amosyu2000/cyclops/src/capture_thread/README.md

<div align="center">

# Capture Button

</div>

## Hardware
[Normally Open Push Button](https://www.amazon.ca/Cylewet-Momentary-Button-Switch-CLT1078/dp/B07DS6QMRW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)

## Usage
In the `src` directory, run `pipenv run python -m capture_thread.__init__`
