amosyu2000/cyclops/docs/Presentations/Rev0Presentation/Rev0_Demo_Slides.pdf

# Cyclops

Real-time bicycle crash detection and blindspot monitoring.

MECHTRON 4TB6 | Rev0 Demo | GitHub (https://github.com/amosyu2000/cyclops) | Team 9 | 1

# What Cyclops offers

1.

### Blindspot Monitoring

MECHTRON 4TB6 | Rev0 Demo | GitHub (https://github.com/amosyu2000/cyclops) | Team 9 | 2

2.

### Convenient Mounting

3.

### Crash Detection

4.

### Video Export

# Blindspot Monitoring

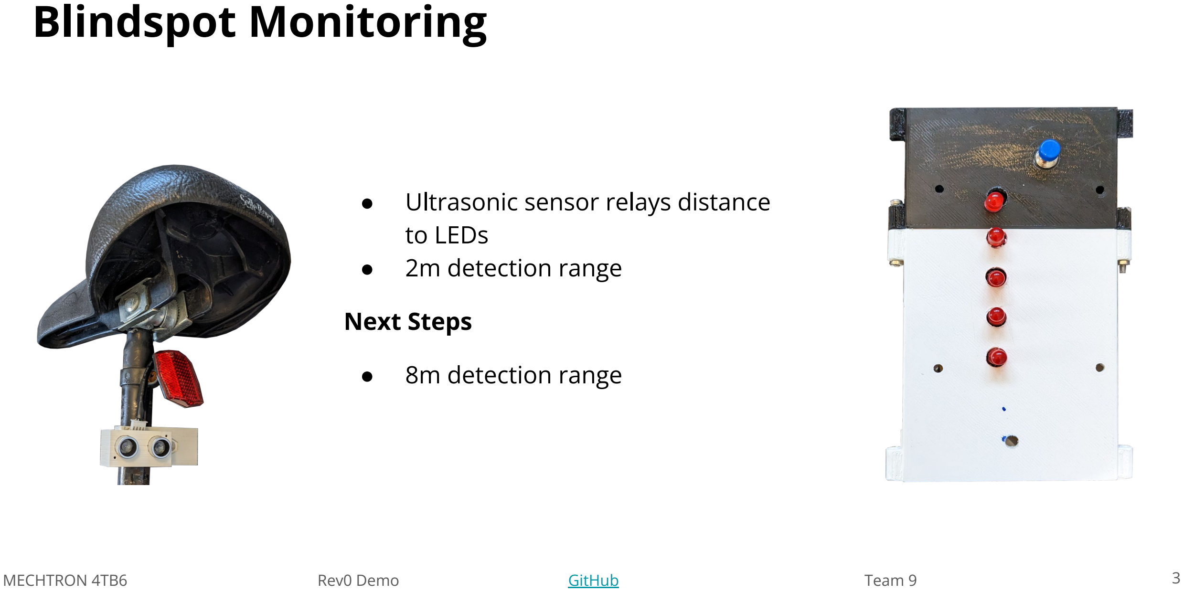
[picture p41: page 3]

- Ultrasonic sensor relays distance to LEDs
- 2m detection range
Next Steps
- 8m detection range
MECHTRON 4TB6 | Rev0 Demo | GitHub (https://github.com/amosyu2000/cyclops) | Team 9 | 3

# Blindspot Monitoring Algorithm

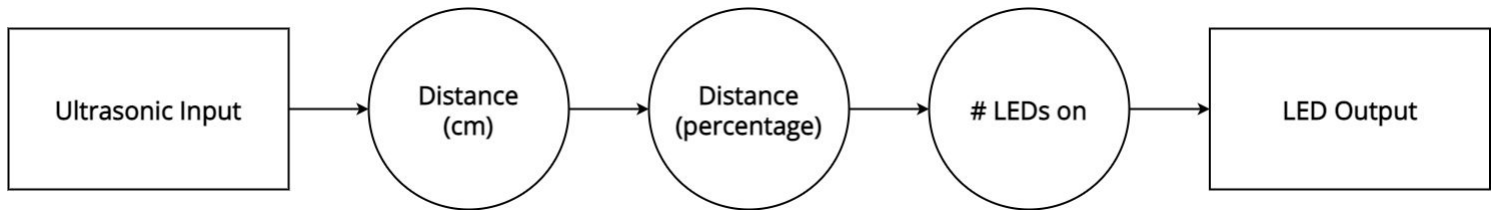
[picture p42: figure]

MECHTRON 4TB6 | Rev0 Demo | GitHub (https://github.com/amosyu2000/cyclops) | Team 9 | 4

# Convenient Mounting

- Turn nut to clamp/release housing
- Keeps together as a single unit
- Rubber grips

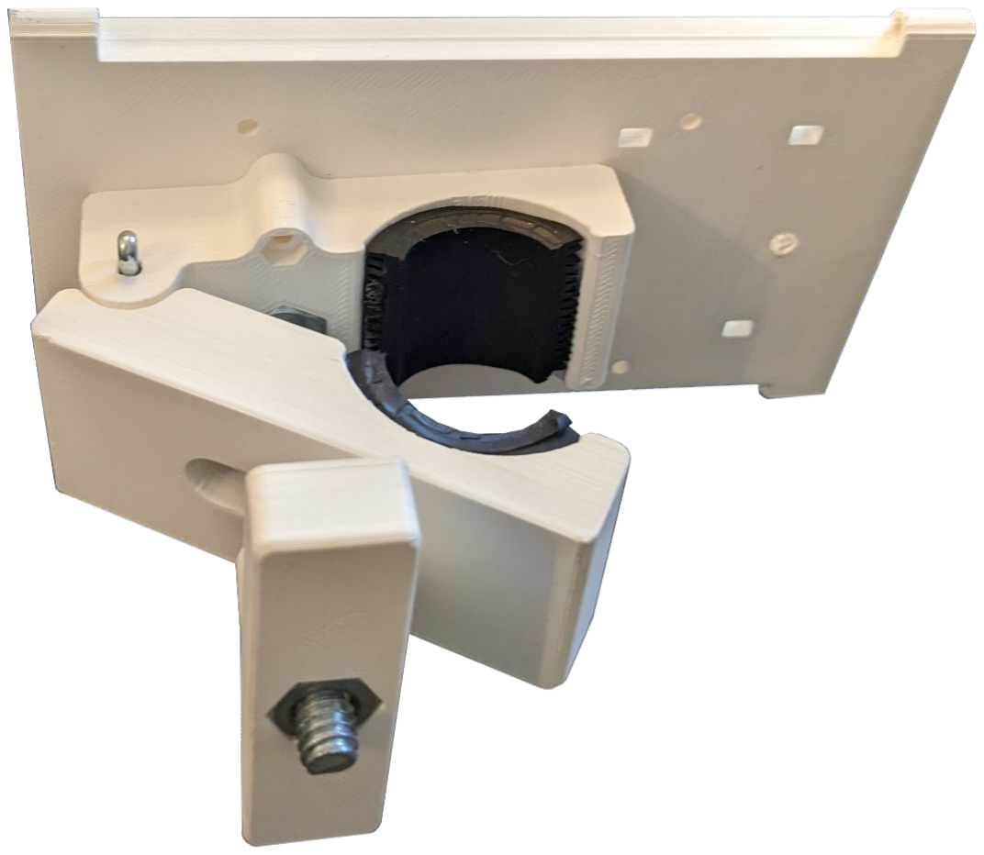
[picture p43: figure]

MECHTRON 4TB6 | Rev0 Demo | GitHub (https://github.com/amosyu2000/cyclops) | Team 9 | 5

# Crash Detection

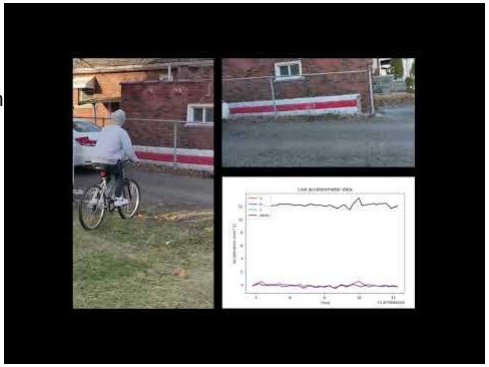
[picture p44: figure]

- Algorithm to interpret accelerometer readings (http://www.youtube.com/watch?v=p9dwgrGUkT8)
- On crash, 60% true positive rate
Next steps
- On crash, 95% true positive rate
- Eliminate false positives
MECHTRON 4TB6 | Rev0 Demo | GitHub (https://github.com/amosyu2000/cyclops) | Team 9 | 6

# Crash Detection Algorithm

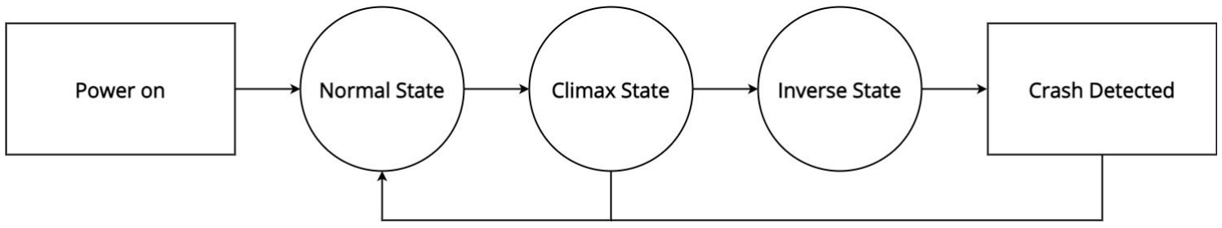
[picture p45: figure]

MECHTRON 4TB6 | Rev0 Demo | GitHub (https://github.com/amosyu2000/cyclops) | Team 9 | 7

# Video Export

- On crash or capture, saves last 60 seconds of video to disk
- Quality is 640p, 24fps
Next Steps
- Save video to thumb drive
- 720p, 30fps
- Decrease CPU utilization

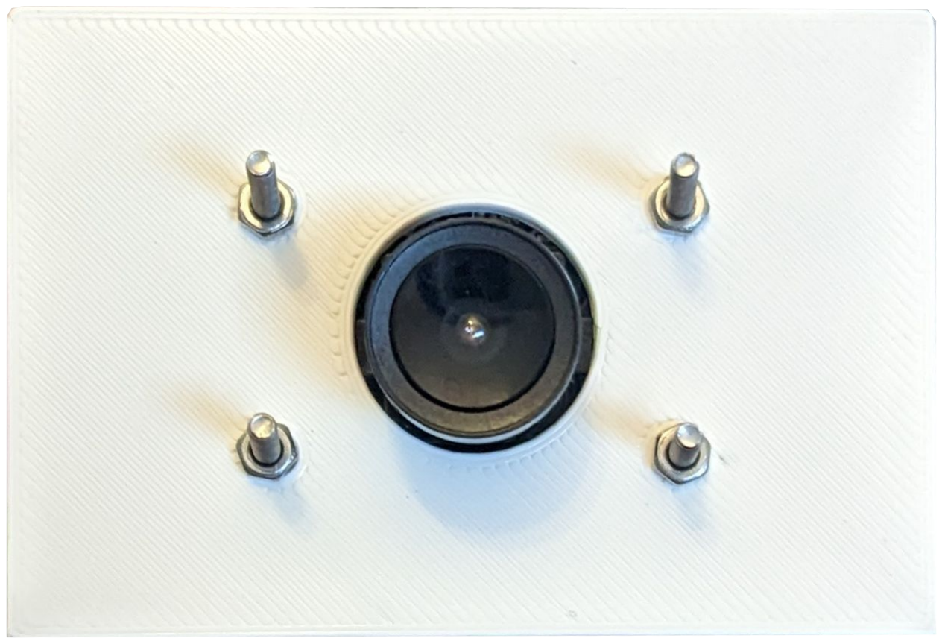
[picture p46: figure]

MECHTRON 4TB6 | Rev0 Demo | GitHub (https://github.com/amosyu2000/cyclops) | Team 9 | 8

# Video Export Algorithm

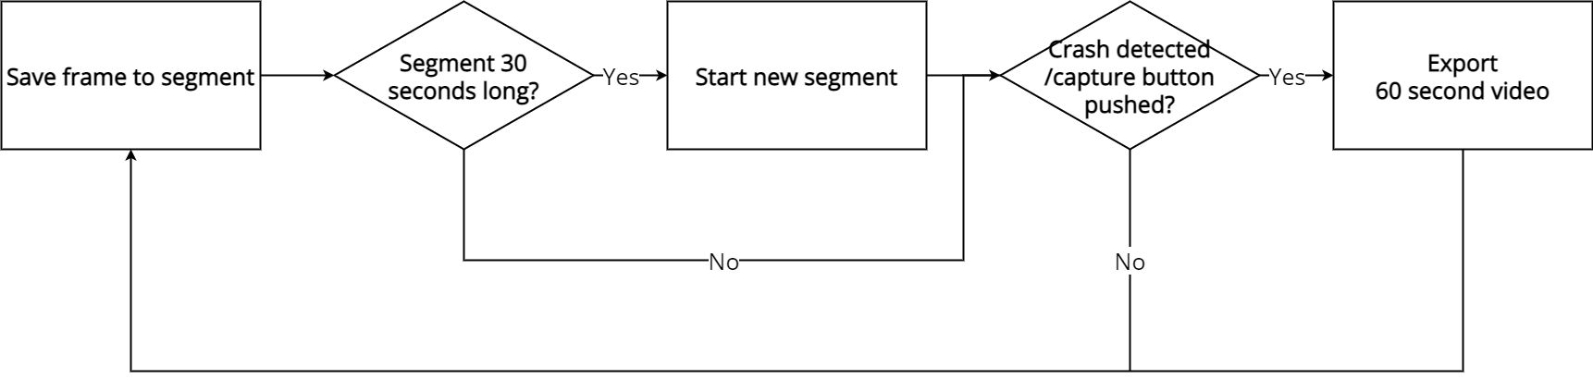
[picture p47: figure]

MECHTRON 4TB6 | Rev0 Demo | GitHub (https://github.com/amosyu2000/cyclops) | Team 9 | 9

# User Interface

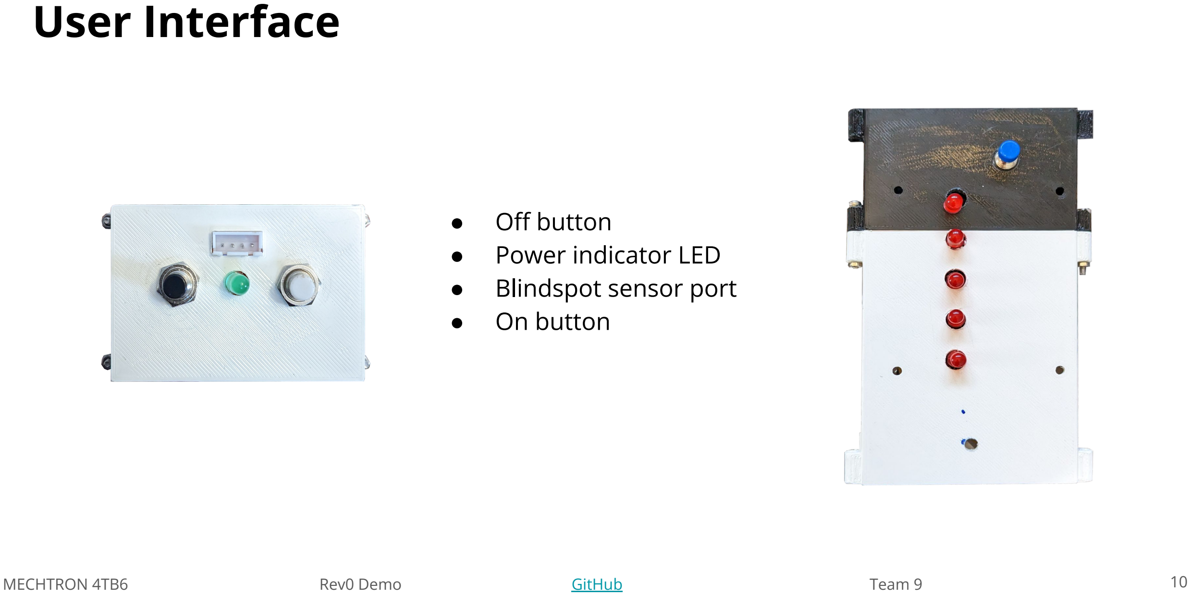
[picture p48: page 10]

- Off button
- Power indicator LED
- Blindspot sensor port
- On button
MECHTRON 4TB6 | Rev0 Demo | GitHub (https://github.com/amosyu2000/cyclops) | Team 9 | 10

# Installation

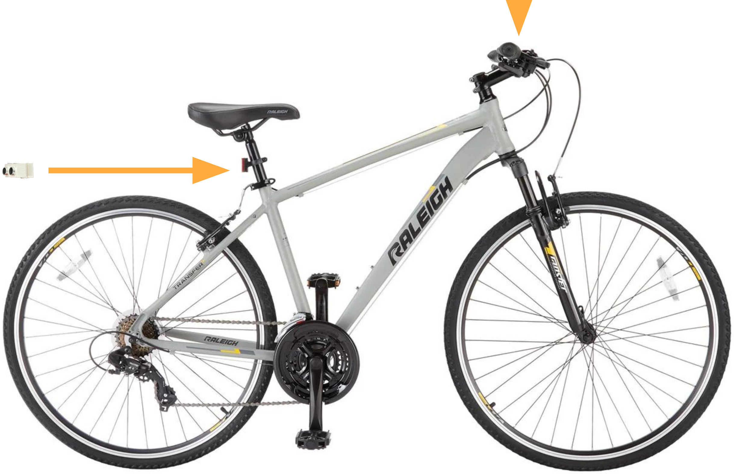
[picture p49: figure]

MECHTRON 4TB6 | Rev0 Demo | GitHub (https://github.com/amosyu2000/cyclops) | Team 9 | 11

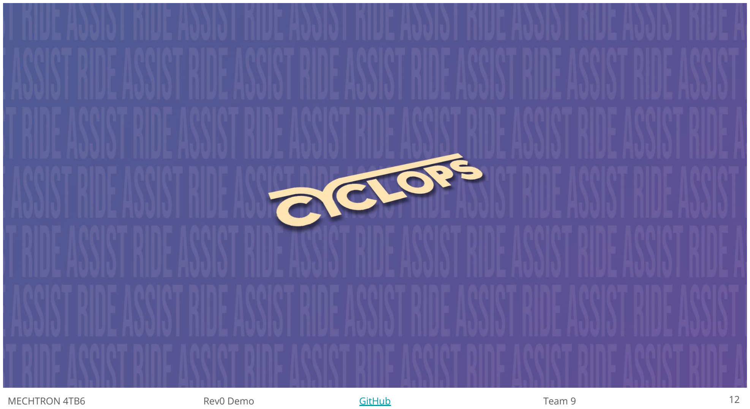
[picture p50: page 12]

MECHTRON 4TB6 | Rev0 Demo | GitHub (https://github.com/amosyu2000/cyclops) | Team 9 | 12
