amosyu2000/cyclops/src/lidar_thread/older_versions/ultrasonic_thread/README.md

<div align="center">

# Ultrasonic Sensor

</div>

## Hardware
[HC-SR04](https://pimylifeup.com/raspberry-pi-distance-sensor/)

## Usage
In the `src` directory, run `pipenv run python -m ultrasonic_thread.__init__`
