amosyu2000/cyclops/src/cad/RASPBERRY PI.stl

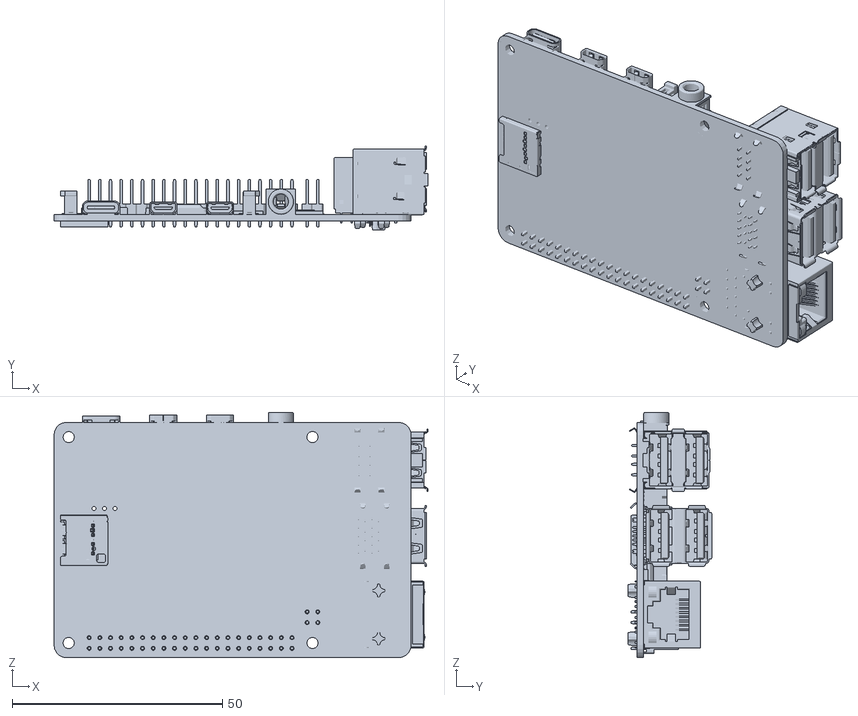
[picture p65: CAD file, 2023-04-05]
src/cad/RASPBERRY PI.stl
89.0 x 19.9 x 58.4
