amosyu2000/cyclops/src/cad/BOLT.stl

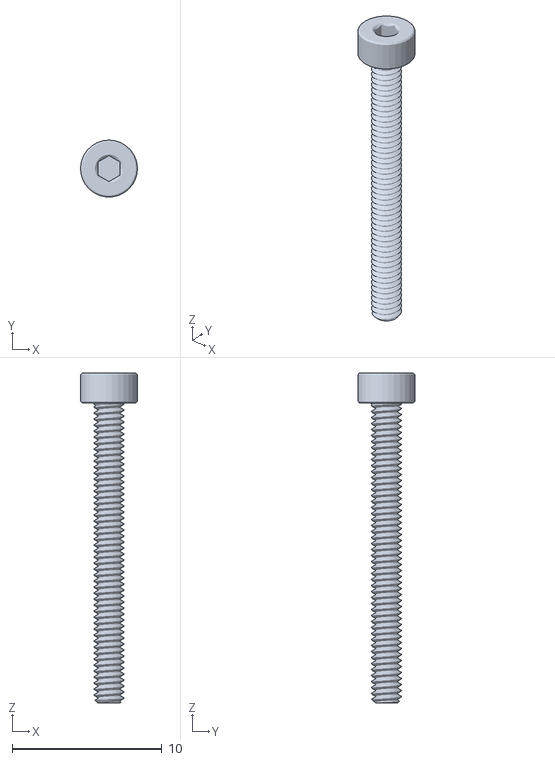
[picture p66: CAD file, 2023-04-05]
src/cad/BOLT.stl
3.79 x 3.79 x 22.0
