amosyu2000/cyclops/src/cad/NUT.stl

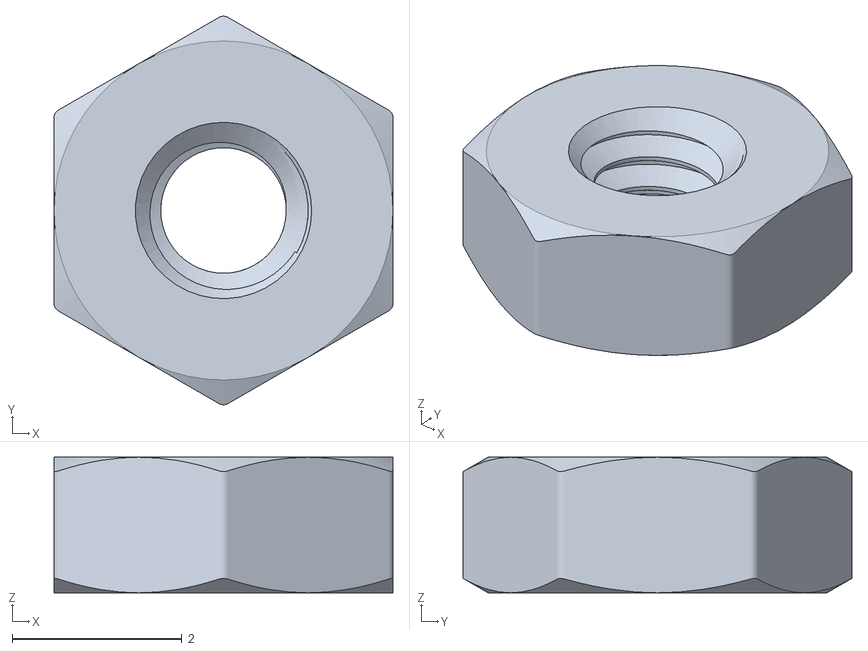
[picture p67: CAD file, 2023-04-05]
src/cad/NUT.stl
4.00 x 4.59 x 1.60
